JPhilC/Sunscan-Crompton-Variant/Images/2025-08-18_09-01-25.jpg

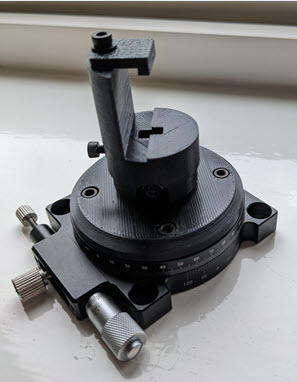
Images/2025-08-18_09-01-25.jpg
