JPhilC/Sunscan-Crompton-Variant/Images/CompactFocuser.jpg

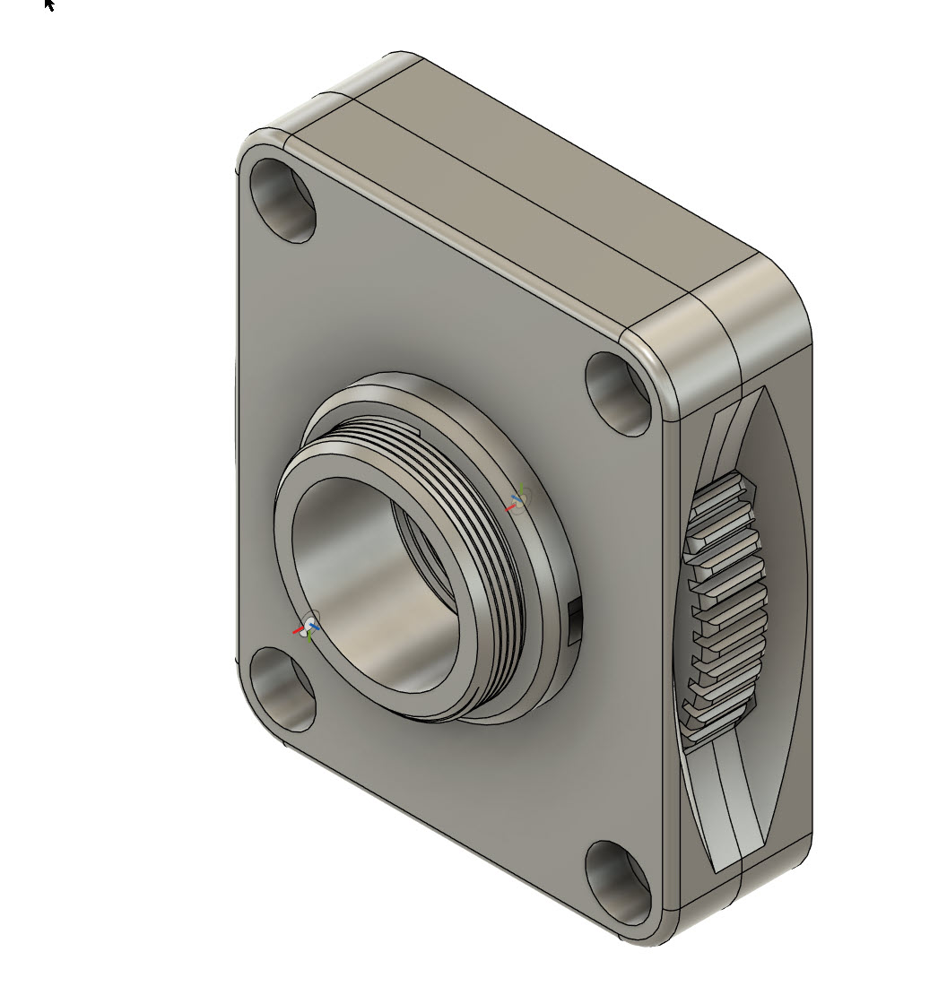
Images/CompactFocuser.jpg
