JPhilC/Sunscan-Crompton-Variant/Images/CompactFocuserSection.jpg

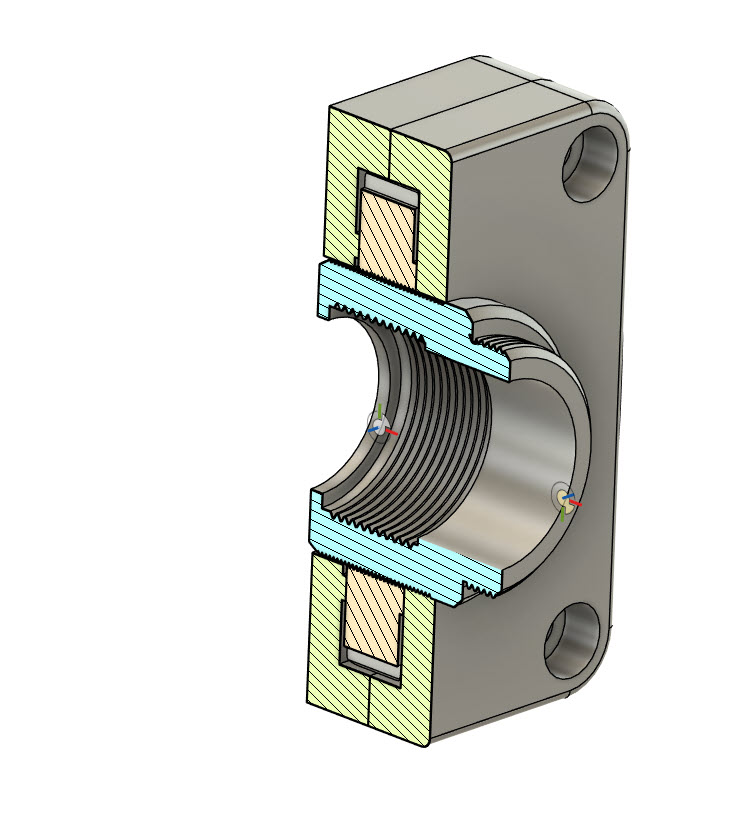
Images/CompactFocuserSection.jpg
