JPhilC/Sunscan-Crompton-Variant/Images/Starting work on case.jpg

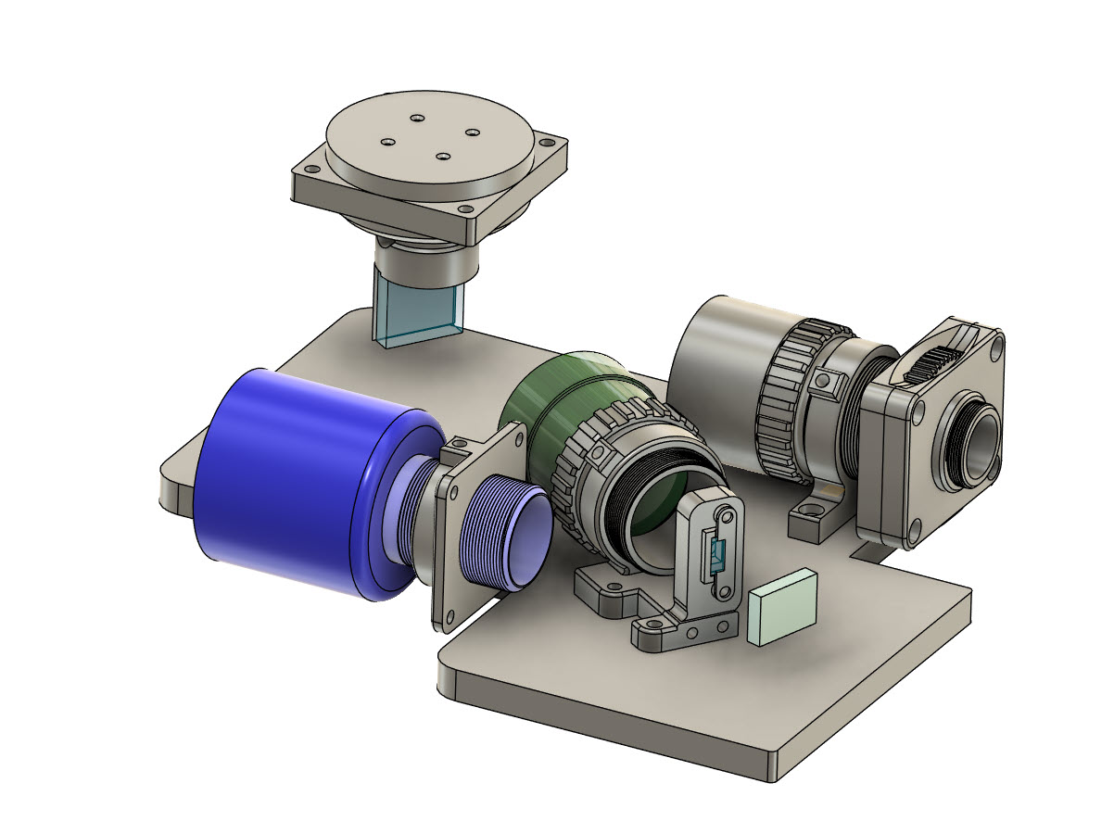
Images/Starting work on case.jpg
