JPhilC/Sunscan-Crompton-Variant/Print Files/Focuser Wheel.3mf

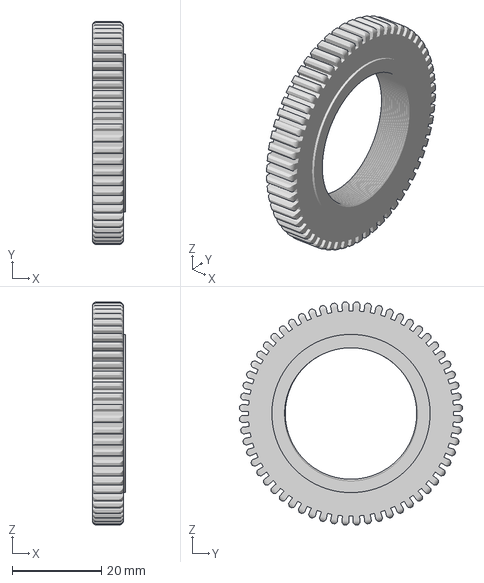
[picture p56: CAD file, 2025-08-26]
Print Files/Focuser Wheel.3mf
7.50 x 50.0 x 50.0 mm
