JPhilC/Sunscan-Crompton-Variant/Print Files/Grating handle.3mf

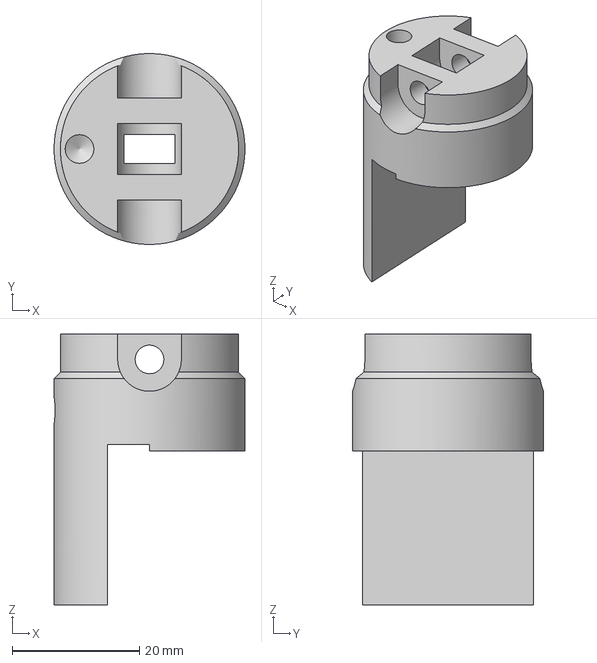
[picture p57: CAD file, 2025-08-26]
Print Files/Grating handle.3mf
30.0 x 30.0 x 42.6 mm
