JPhilC/Sunscan-Crompton-Variant/Print Files/Grating base (alt).3mf

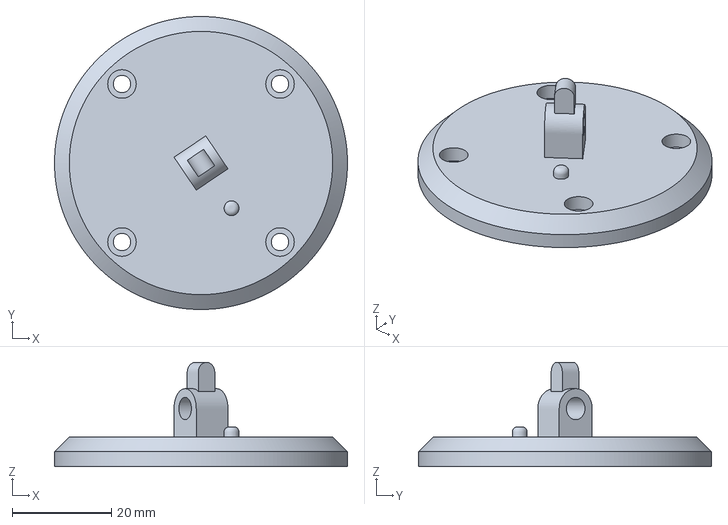
[picture p58: CAD file, 2025-08-26]
Print Files/Grating base (alt).3mf
59.0 x 59.0 x 21.0 mm
