JPhilC/Sunscan-Crompton-Variant/Print Files/Camera Lens Bench.3mf

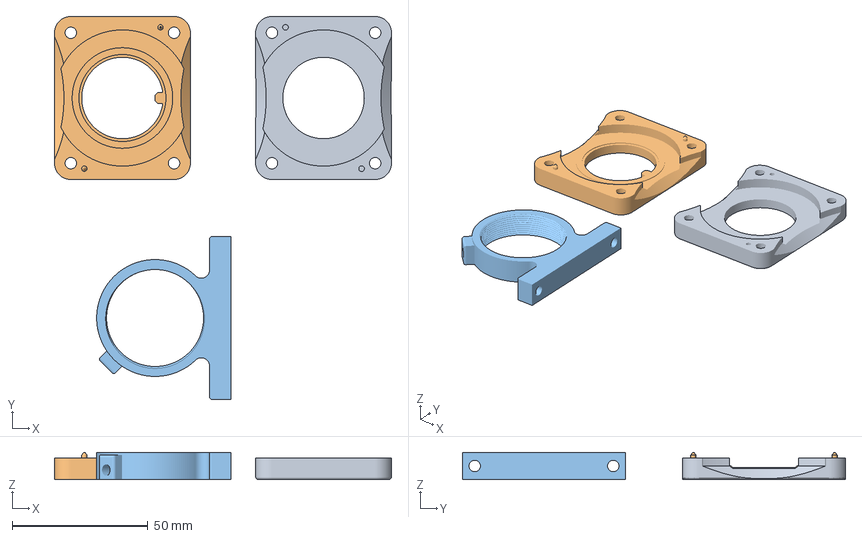
[picture p59: CAD file, 2025-08-26]
Print Files/Camera Lens Bench.3mf
124.0 x 141.0 x 10.0 mm
HF Body Front
HF Body Back
CameraLensBench
