JPhilC/Sunscan-Crompton-Variant/Print Files/M31 Interface block.3mf

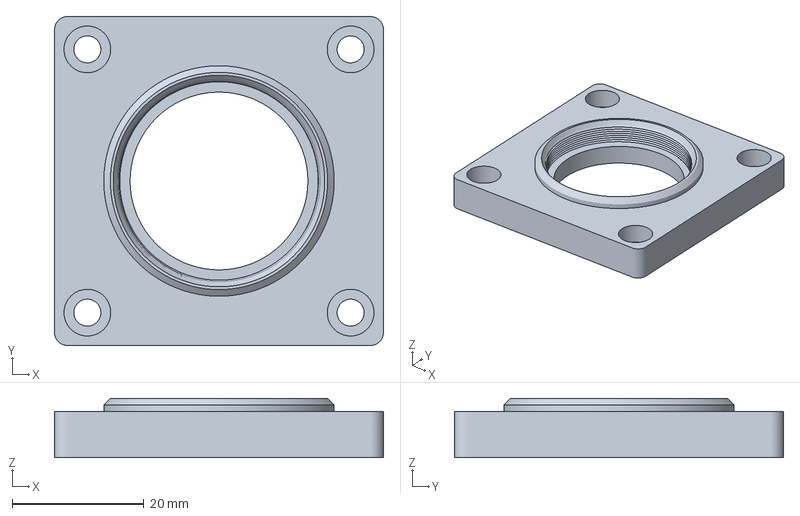
[picture p60: CAD file, 2025-08-26]
Print Files/M31 Interface block.3mf
50.0 x 50.0 x 9.00 mm
