JPhilC/Sunscan-Crompton-Variant/Print Files/Objective Bench.3mf

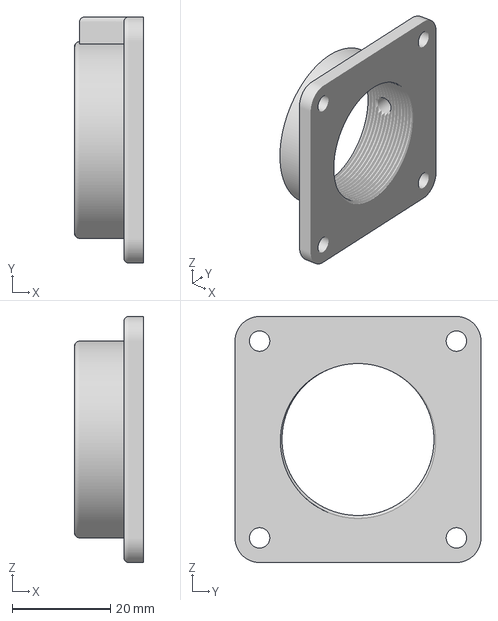
[picture p61: CAD file, 2025-08-26]
Print Files/Objective Bench.3mf
14.0 x 50.0 x 50.0 mm
