JPhilC/Sunscan-Crompton-Variant/Print Files/Grating Holder.3mf

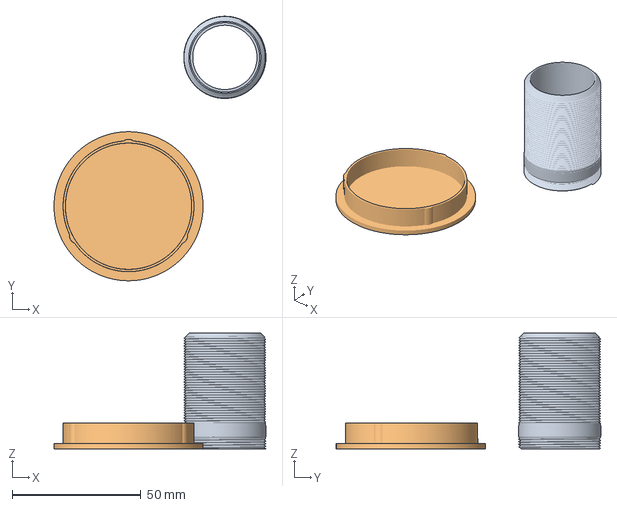
[picture p62: CAD file, 2025-08-26]
Print Files/Grating Holder.3mf
82.5 x 102.9 x 45.0 mm
Focus tube
Lens Cap
