JPhilC/Sunscan-Crompton-Variant/Print Files/Objective Focus tube.3mf

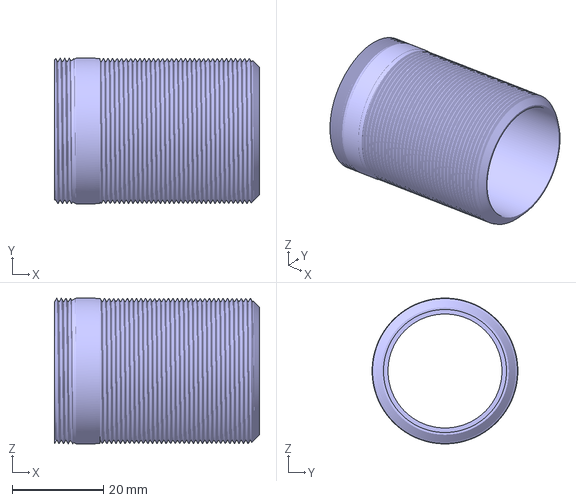
[picture p63: CAD file, 2025-08-26]
Print Files/Objective Focus tube.3mf
45.0 x 32.0 x 32.0 mm
