JPhilC/Sunscan-Crompton-Variant/Print Files/Indicator Disc Spacer.3mf

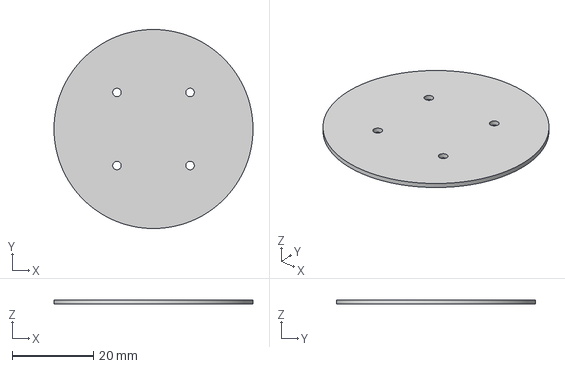
[picture p64: CAD file, 2025-08-26]
Print Files/Indicator Disc Spacer.3mf
49.0 x 49.0 x 1.00 mm
