JPhilC/Sunscan-Crompton-Variant/Print Files/Infinity Hole Cover.3mf

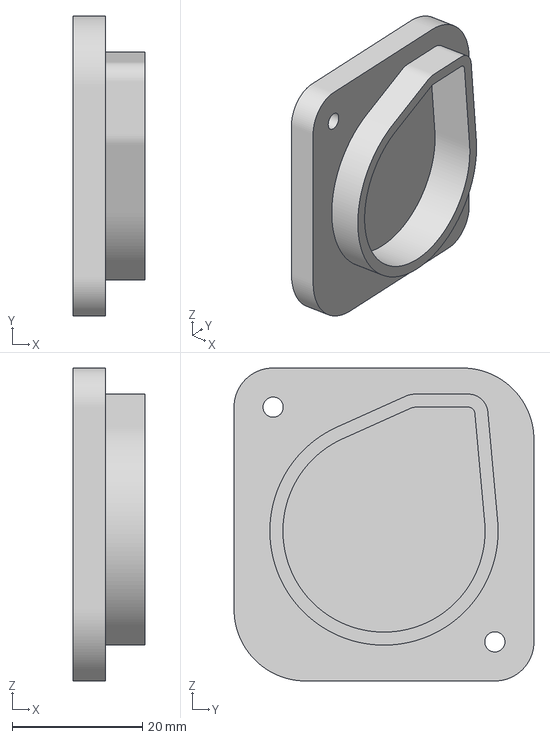
[picture p65: CAD file, 2025-08-26]
Print Files/Infinity Hole Cover.3mf
11.0 x 46.0 x 48.0 mm
