JPhilC/Sunscan-Crompton-Variant/Print Files/Objective Spacer Ring.3mf

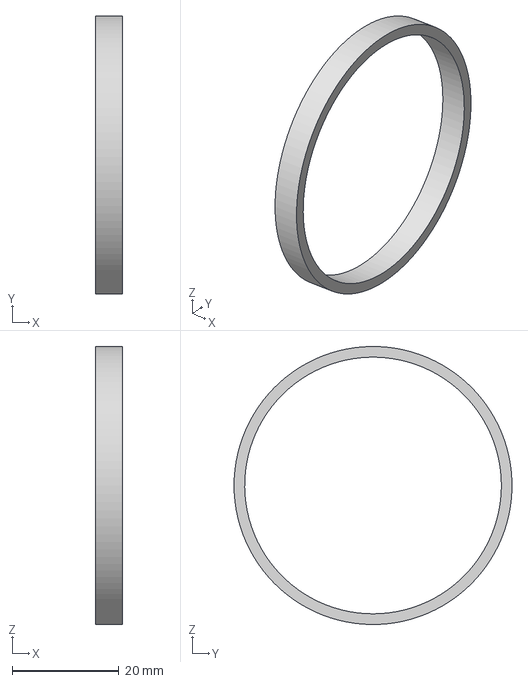
[picture p66: CAD file, 2025-08-26]
Print Files/Objective Spacer Ring.3mf
5.00 x 52.0 x 52.0 mm
