JPhilC/Sunscan-Crompton-Variant/Print Files/Slit cover.3mf

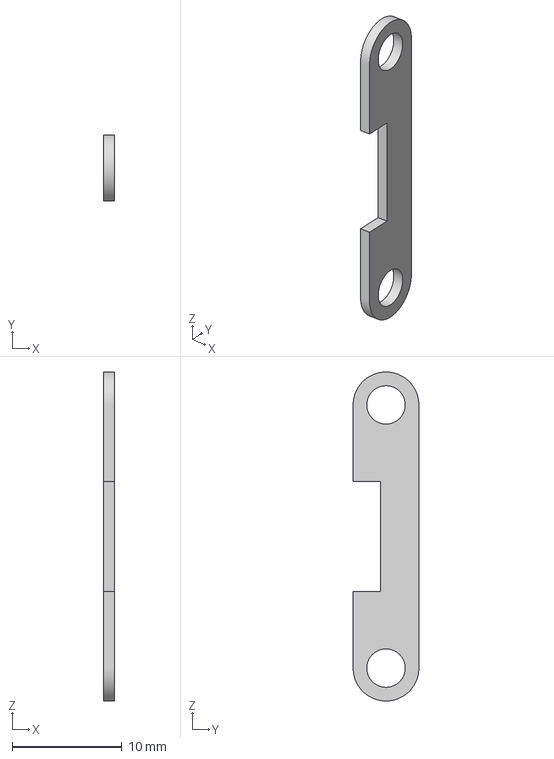
[picture p67: CAD file, 2025-08-26]
Print Files/Slit cover.3mf
1.00 x 6.00 x 30.0 mm
