JPhilC/Sunscan-Crompton-Variant/Print Files/Collimator Bench.3mf

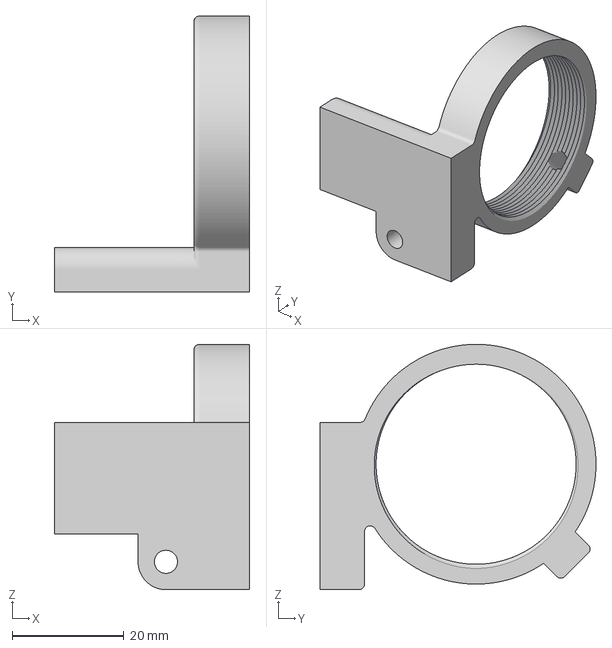
[picture p68: CAD file, 2025-08-26]
Print Files/Collimator Bench.3mf
35.0 x 49.5 x 44.0 mm
