JPhilC/Sunscan-Crompton-Variant/Print Files/Cap Filter Holder.3mf

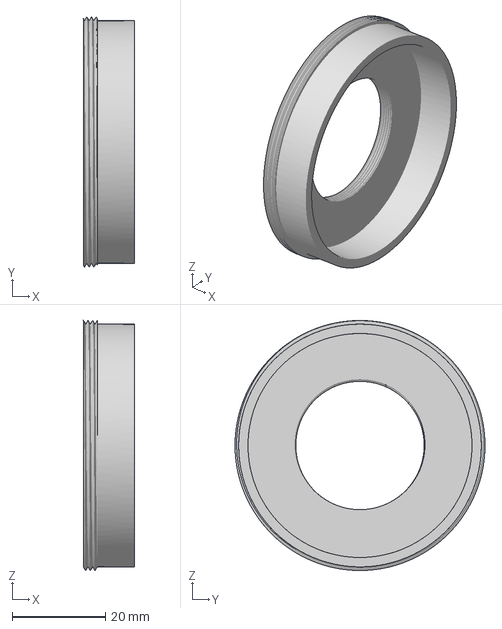
[picture p69: CAD file, 2025-08-26]
Print Files/Cap Filter Holder.3mf
11.0 x 53.6 x 53.6 mm
