JPhilC/Sunscan-Crompton-Variant/Print Files/M39 lens focus tube.3mf

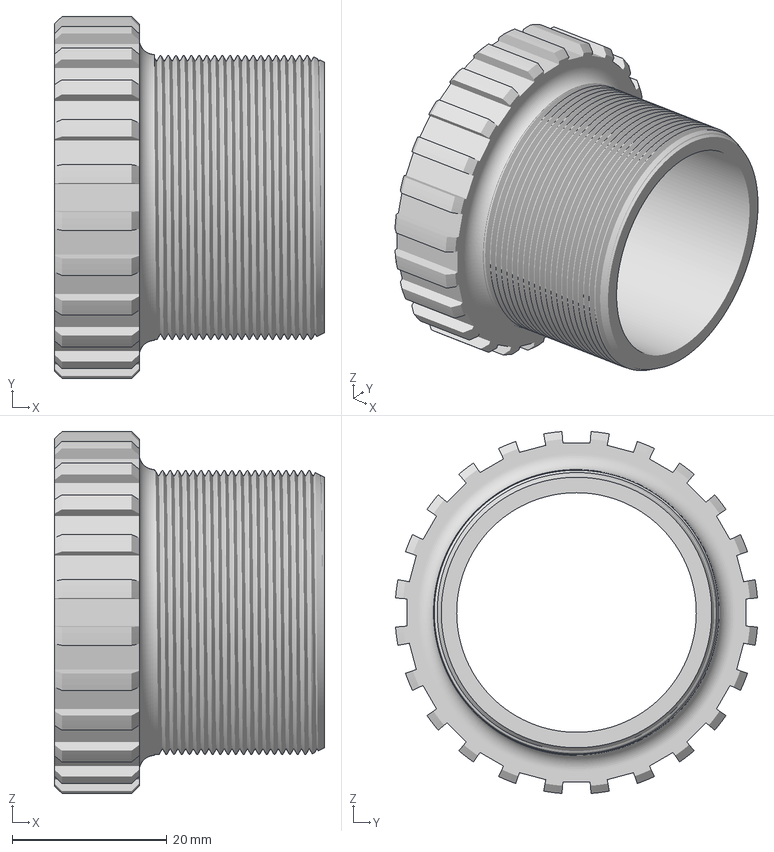
[picture p70: CAD file, 2025-08-26]
Print Files/M39 lens focus tube.3mf
35.0 x 46.8 x 46.8 mm
