JPhilC/Sunscan-Crompton-Variant/Print Files/Focuser Body Back.3mf

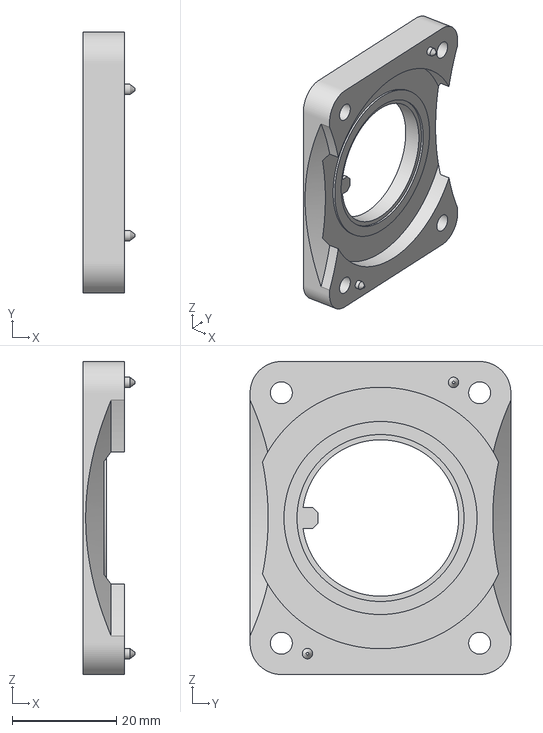
[picture p71: CAD file, 2025-08-26]
Print Files/Focuser Body Back.3mf
10.0 x 50.0 x 60.0 mm
