JPhilC/Sunscan-Crompton-Variant/Print Files/Objective Lens Housing.3mf

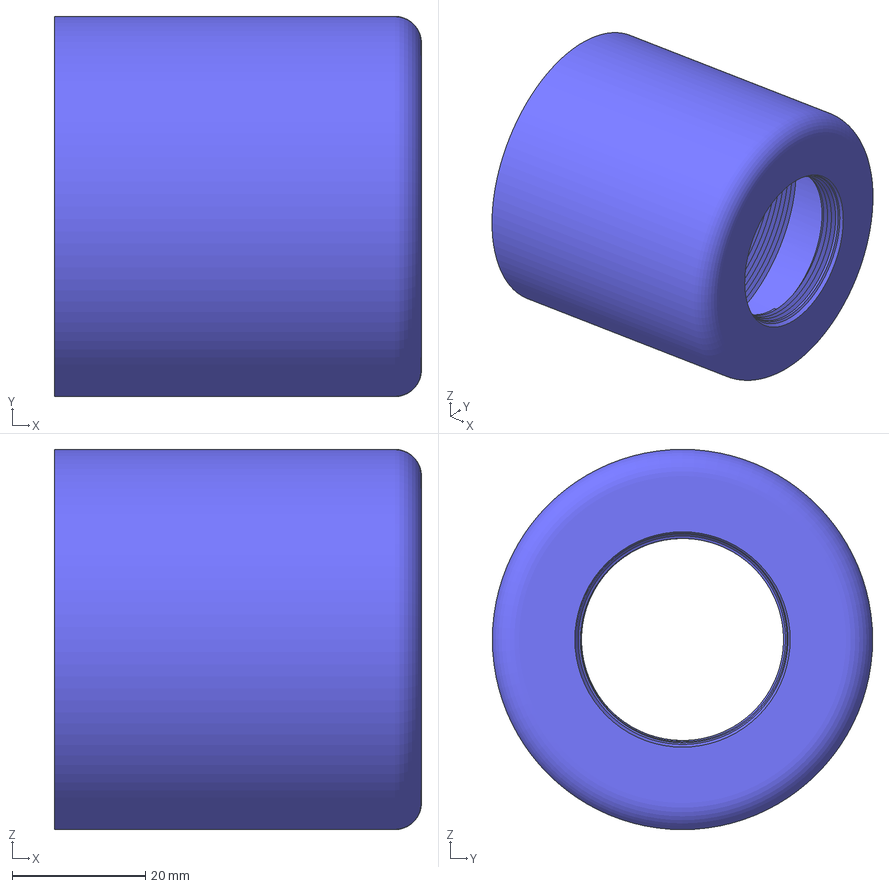
[picture p72: CAD file, 2025-08-26]
Print Files/Objective Lens Housing.3mf
55.0 x 57.0 x 57.0 mm
