JPhilC/Sunscan-Crompton-Variant/Print Files/Turntable Platform.3mf

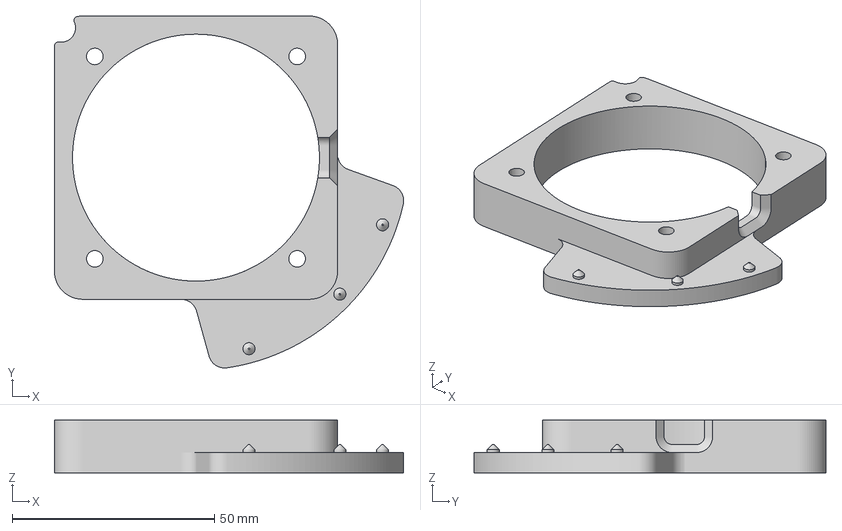
[picture p73: CAD file, 2025-08-26]
Print Files/Turntable Platform.3mf
86.3 x 87.0 x 13.0 mm
