JPhilC/Sunscan-Crompton-Variant/Print Files/Indicator Disc.3mf

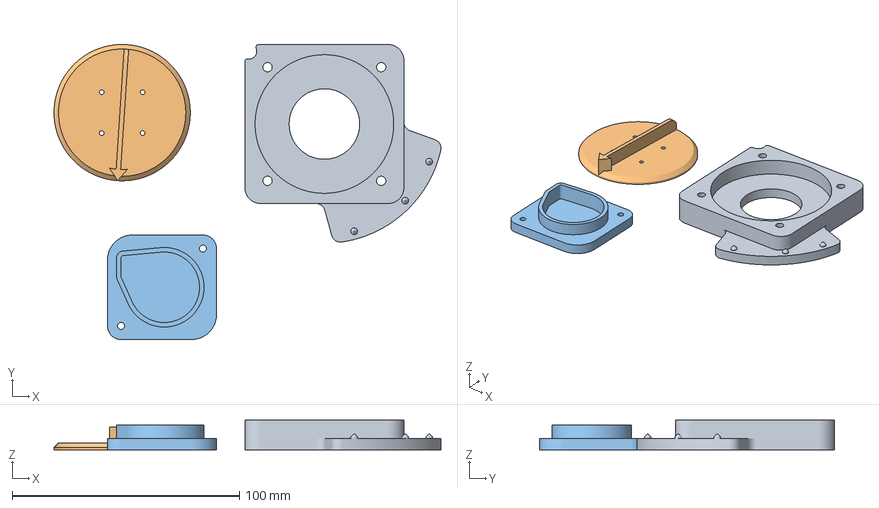
[picture p74: CAD file, 2025-08-26]
Print Files/Indicator Disc.3mf
170.3 x 129.8 x 13.0 mm
Turntable Platform
IndicatorDisk
FocusHoleCover
