JPhilC/Sunscan-Crompton-Variant/Print Files/Slit Bench.3mf

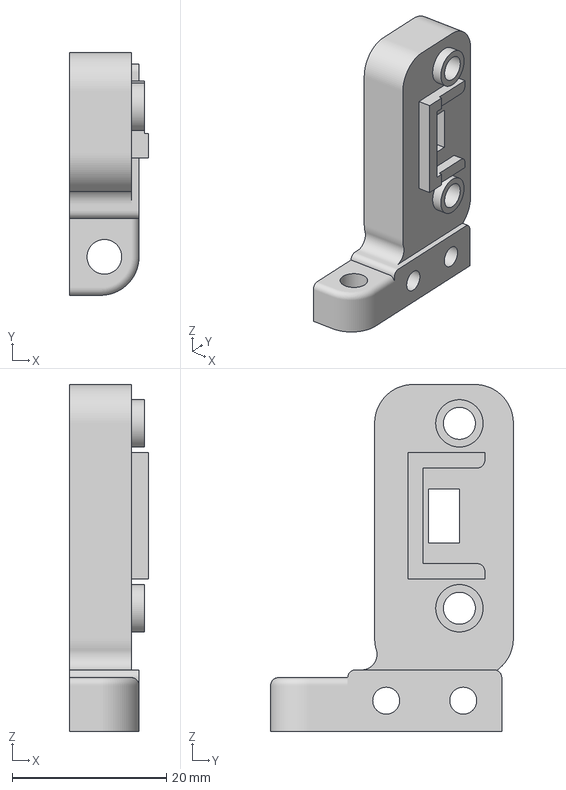
[picture p75: CAD file, 2025-08-26]
Print Files/Slit Bench.3mf
10.2 x 31.5 x 45.0 mm
